guillecade22/ShotBot/assets/interior.jpg

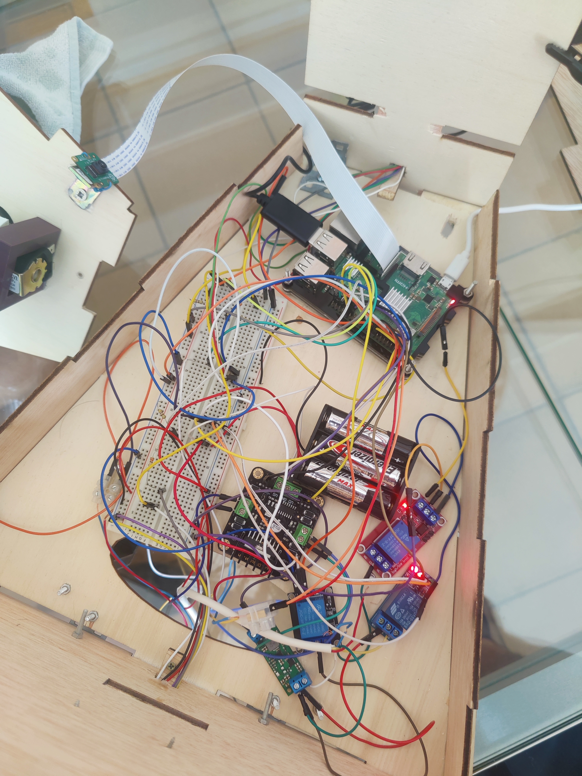
assets/interior.jpg
