guillecade22/ShotBot/src/display/shots.png

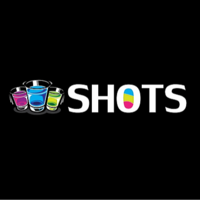
src/display/shots.png
